alexpantone/croissant/Configuration Guides/Croissant Minimal Config.jpg

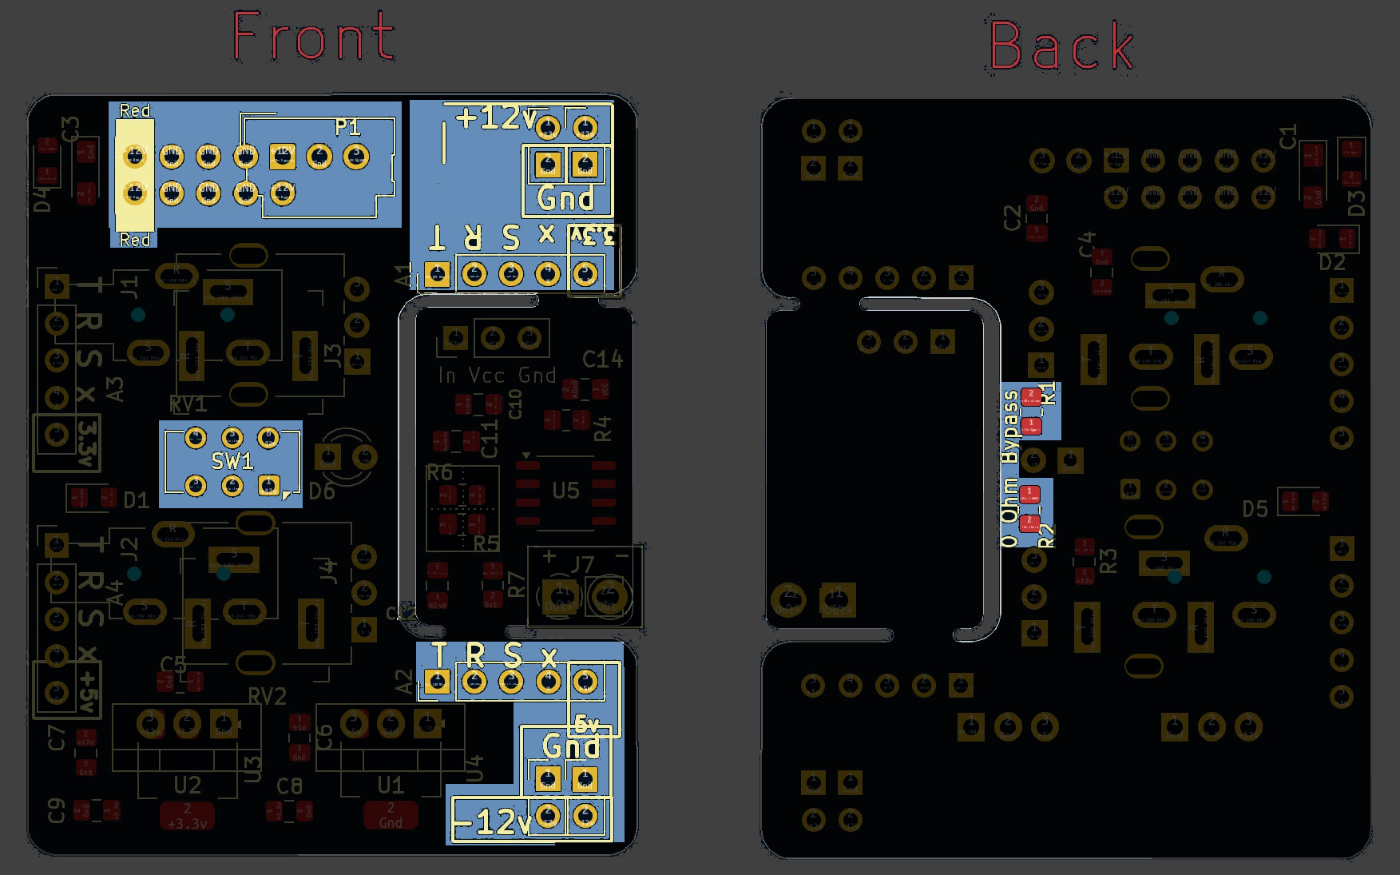
Configuration Guides/Croissant Minimal Config.jpg
